chillu/arduino-led-scarf/src/PatternState.h

#ifndef PatternState_h
#define PatternState_h

/**
 * Provides shared state between patterns.
 * State for a pattern can be memory intensive and with only 2KB of SRAM availble,
 * it's not practical to have separate state for each pattern.
 *
 * Rather than use globals, we make use of a PatternState object.
 *
 * @author Sam Minnee
 */
class PatternState {
  protected:
    /**
     * A byte that can be used to track 'activation level' per LED
     * Patterns can use this as they wish
     */
    byte *activation;

  public:
    /**
     * The LEDs to write to
     */
    CRGB *leds;

    byte ledsSize;

    /**
     * A palette to for the patterns to use.
     */
    CRGBPalette16 *palette;

    PatternState(byte _ledsSize, CRGB *_leds): activation(0)
    {
      ledsSize = _ledsSize;

      leds = _leds;
      for(byte i = 0; i < ledsSize; i++) {
        leds[i] = CRGB::Black;
      }
    };

    byte *getActivation()
    {
      // Allocate the byte array if it hasn't realy been allocated
      if ((unsigned int)activation == 0) {
        Serial.println("Allocating activation");
        activation = new byte[ledsSize];
        for(byte i = 0; i < ledsSize; i++) {
          activation[i] = 0;
        }
      }

      return activation;
    };

};

#endif
