chillu/arduino-led-scarf/src/Plasma.h

#include "Pattern.h"

/**
 * Sine wave (single factor plasma) that moves up the strip
 */
class Plasma: public Pattern {
  public:
    void loopForState(PatternState *state, byte fade)
    {
      for (int i = 0; i < state->ledsSize; i++) {
        byte c = sin8((long) i * 30 - millis() / 2);
        byte colorindex = scale8(c, 200);
        state->leds[i] = ColorFromPalette(*state->palette, colorindex);
      }
    }
};
